breadwinner-life/community-hardware/constants.h

#define API_ENDPOINT "breadwinner.life"
#define API_PORT 80
#define API_PATH "/api/v1/"
#define HEALTH_ENDPOINT "/health"

#define DEVICE_ID <YOUR DEVICE_ID>

#define UPLOAD_BATCH_SIZE 25
#define UPLOADS_PER_HOUR 4
#define SAMPLES_PER_MINUTE 4
#define PINGS_PER_MINUTE 1

#define VITALS "vitals"
#define FEEDINGS "feedings"
